cmu-devlab/botero-3d-printer/printer-parts/t-slot-cable-cover/t-slot_cable_cover_v2.stl

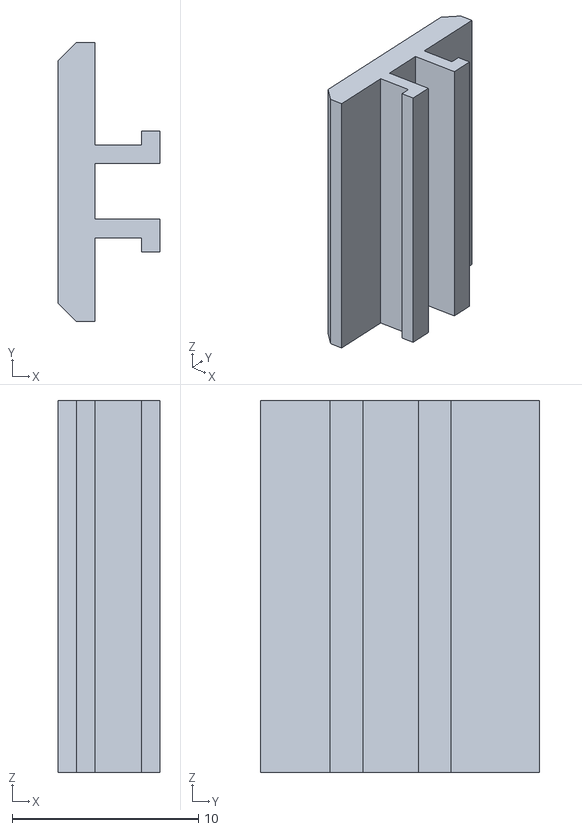
[picture p15: CAD file, 2016-07-10]
printer-parts/t-slot-cable-cover/t-slot_cable_cover_v2.stl
5.50 x 15.0 x 20.0
