cmu-devlab/botero-3d-printer/printer-parts/led-holder/led_brackets_v2.stl

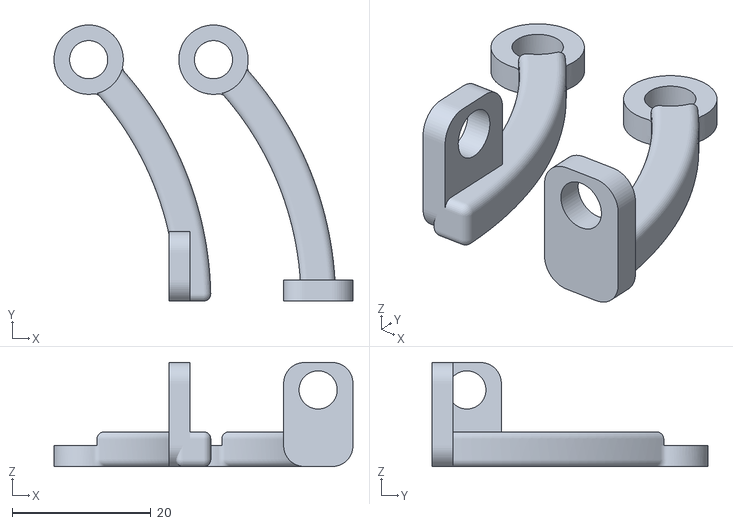
[picture p16: CAD file, 2016-07-10]
printer-parts/led-holder/led_brackets_v2.stl
43.1 x 39.8 x 15.0
